CasamaMaker/eLoad/firmware/screenshots/burnMultipleFiles.png

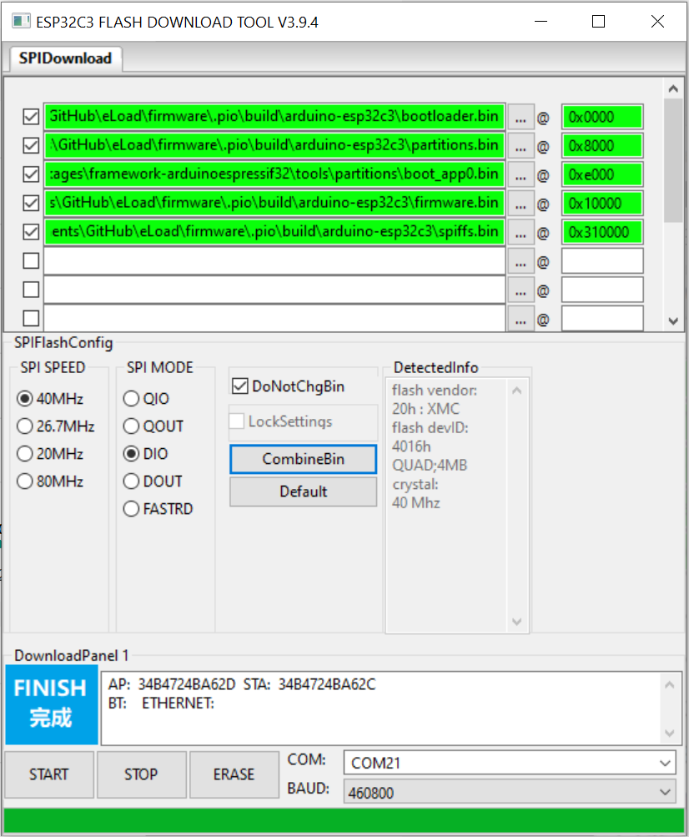
firmware/screenshots/burnMultipleFiles.png
