CasamaMaker/eLoad/firmware/screenshots/burnProgramPlatformIO.png

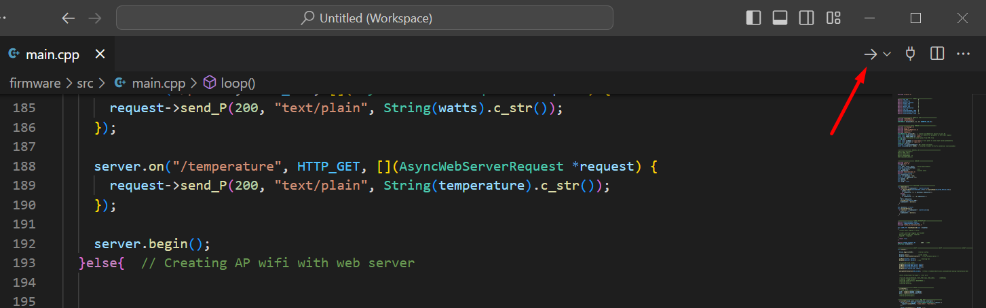
firmware/screenshots/burnProgramPlatformIO.png
