CasamaMaker/eLoad/firmware/screenshots/burnSpiffsPlatformIO.png

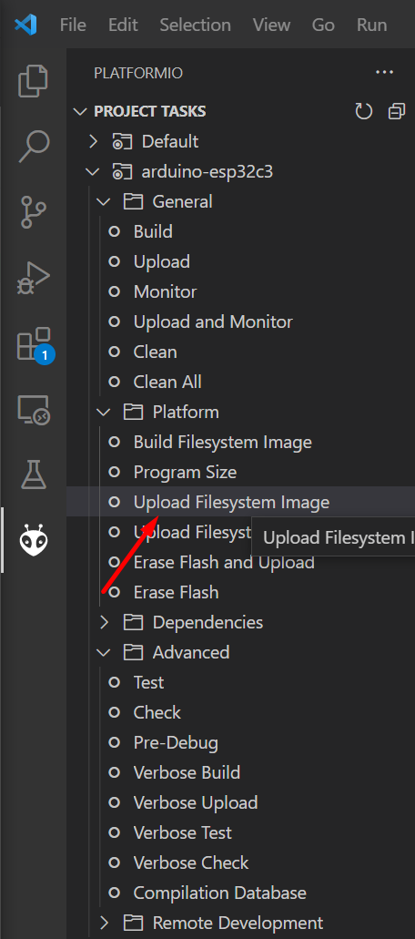
firmware/screenshots/burnSpiffsPlatformIO.png
