CasamaMaker/eLoad/hardware/pictures/picture3.jpg

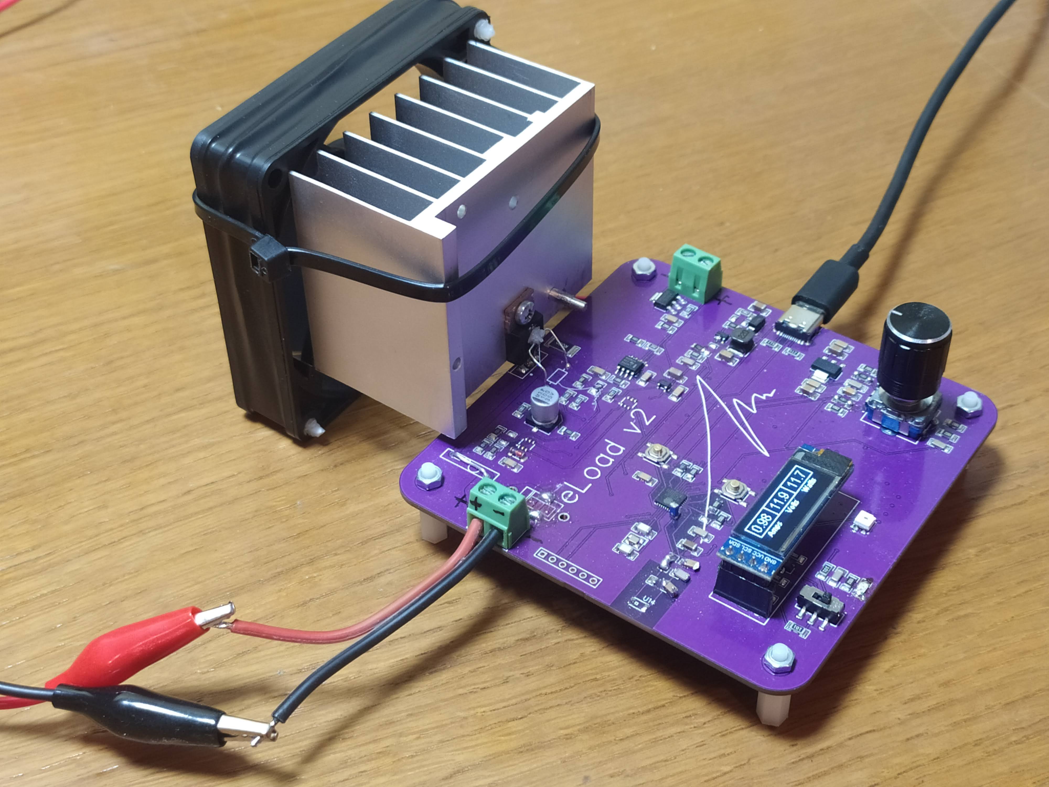
hardware/pictures/picture3.jpg
