CasamaMaker/eLoad/firmware/src/wifimanager.h

#ifndef WIFIMANAGER_H
#define WIFIMANAGER_H

#include <Arduino.h>
#include <WiFi.h>
#include <ESPAsyncWebServer.h>
#include <AsyncTCP.h>
#include "SPIFFS.h"

void initSPIFFS();
String readFile(fs::FS &fs, const char * path);
void writeFile(fs::FS &fs, const char * path, const char * message);
bool initWiFi(String ssid, String pass, unsigned long previousMillis, const long interval);
String processor(const String& var);

#endif
